fabiobaltieri/usb-current-meter/firmware-nrf/main.c

/*
 * Copyright 2011 Fabio Baltieri <fabio.baltieri@gmail.com>
 *
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
 */

#include <stdint.h>
#include <avr/io.h>
#include <avr/sleep.h>
#include <avr/wdt.h>
#include <avr/interrupt.h>
#include <util/delay.h>

#include "board.h"

#include "id.h"
#include "spi.h"
#include "adc.h"
#include "nrf24l01p.h"

#include "nrf_frames.h"

#define div_round(a, b) (((a) + ((b)/2)) / (b))

static struct nrf_frame pkt;

static void hello(void)
{
	uint8_t i;

	for (i = 0; i < 9; i++) {
		led_a_toggle();
		_delay_ms(50);
	}
}

static uint16_t get_power(void)
{
	uint32_t value;
	uint16_t offset;
	uint8_t gain;

	offset = 0;
	value  = adc_get(ADC_COIL);

	if (value < AMP_TH) {
		offset = adc_get(ADC_OFFSET_20X);
		value  = adc_get(ADC_COIL_20X);
		gain = 20;
	} else {
		gain = 1;
	}

	if (value < offset)
		value = 0;
	else
		value = div_round((value - offset) * ADC_VREF_mV * CAL_POWER,
				ADC_VREF_BITS * CAL_VOLTAGE * (uint32_t)gain);

	return value;
}

/* RF_IRQ */
ISR(INT0_vect)
{
	nrf_irq();

	led_a_off();
}

ISR(WDT_vect)
{
	uint16_t val;
	struct nrf_power *pwr = &pkt.msg.power;

	adc_init();
	val = get_power();
	pwr->value[3] = -1;
	pwr->value[2] = -1;
	pwr->value[1] = -1;
	pwr->value[0] = val;

	val = adc_get(ADC_VCC);
	val = div_round(1100l * 1024, val);
	pwr->vbatt = val;
	adc_stop();

	if (is_charging())
		pwr->vbatt |= NRF_POWER_VBATT_CHARGING;

	nrf_standby();
	nrf_tx((uint8_t *)&pkt, sizeof(pkt));

	led_a_on();

	pkt.seq++;
}

int main(void)
{
	read_board_id();

	led_init();
	analog_init();
	spi_init();
	chg_init();

	led_a_on();
	analog_on();

	/* IO init */
	NRF_DDR |= _BV(NRF_CS) | _BV(NRF_CE);
	nrf_cs_h();
	nrf_ce_l();

	nrf_init();

	PRR = _BV(PRTIM1) | _BV(PRTIM0) | _BV(PRUSI);

	/* WDT as periodic interrupt */
	WDTCSR |= (1 << WDE) | (1 << WDCE);
	WDTCSR = (0 << WDCE) | (1 << WDIF) | (1 << WDIE) |
		 (1 << WDP2) | (1 << WDP1) | (0 << WDP0);

	/* INT0 init - low level */
	GIMSK |= (1 << INT0);
	MCUCR |= (0 << ISC01) | (0 << ISC00);

	hello();
	sei();

	pkt.board_id = get_board_id();
	pkt.msg_id = NRF_MSG_ID_POWER;
	pkt.len = 16;
	pkt.seq = 0;

	while (1) {
		set_sleep_mode(SLEEP_MODE_PWR_DOWN);
		sleep_mode();
	}
}
